McOrts/MKRFOX1200_mobile-weather-station/cell_app.png

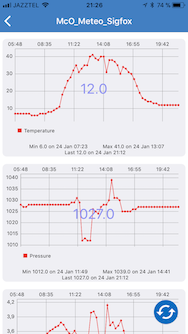
cell_app.png
