McOrts/MKRFOX1200_mobile-weather-station/MKRFOX1200_mobile-weather-station_report-data/MKRFOX1200_location_Spain_Mallorca_Palma_201711.png

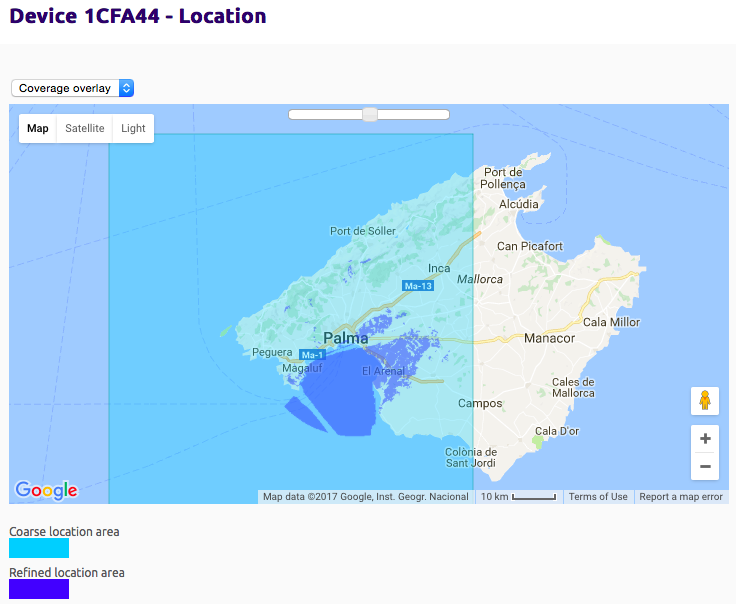
MKRFOX1200_mobile-weather-station_report-data/MKRFOX1200_location_Spain_Mallorca_Palma_201711.png
